rpbarnes/PI_Blackbox/PCB/FAB_Files/Assembled_Pics/bottom001.png

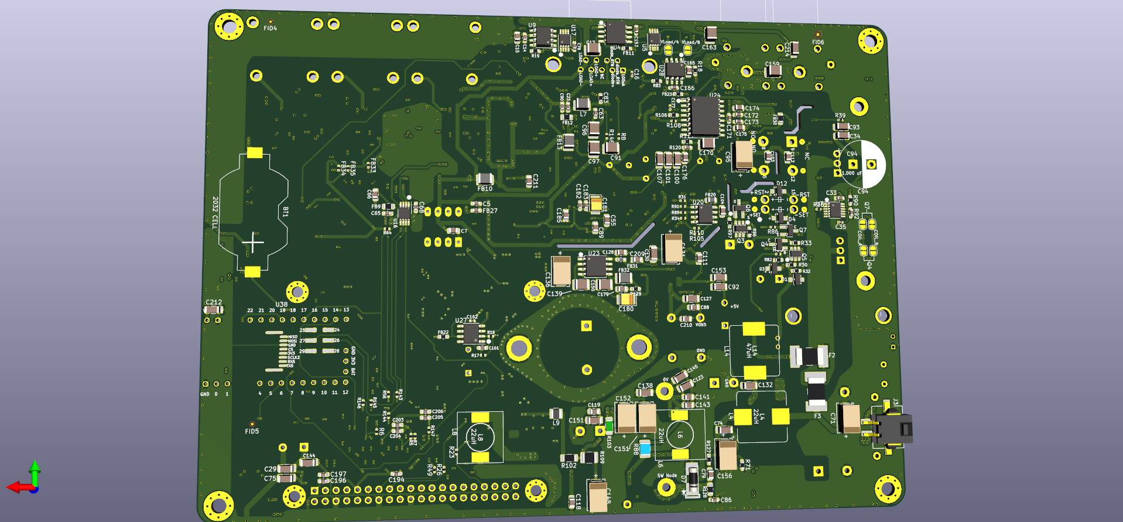
PCB/FAB_Files/Assembled_Pics/bottom001.png
