rpbarnes/PI_Blackbox/PCB/FAB_Files/Assembled_Pics/bottom002.png

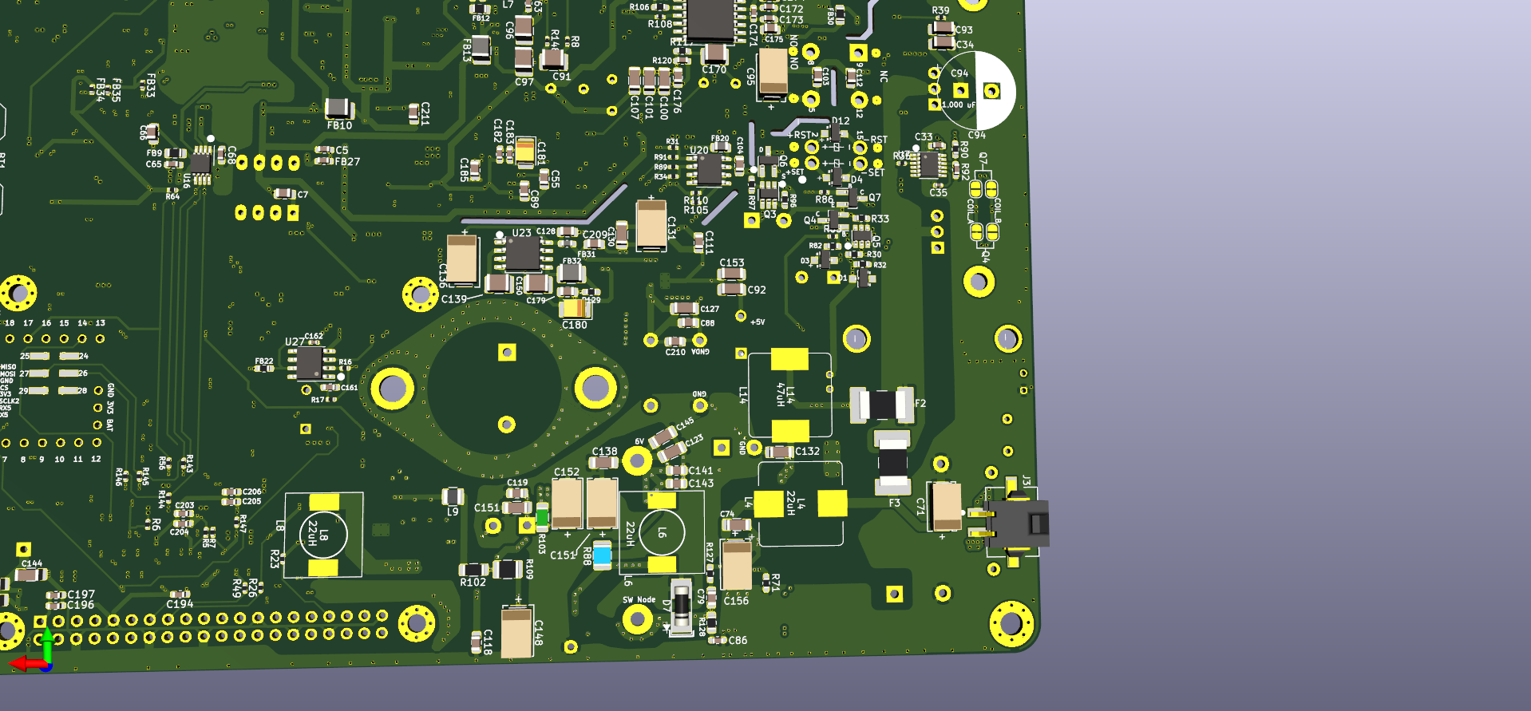
PCB/FAB_Files/Assembled_Pics/bottom002.png
