rpbarnes/PI_Blackbox/PCB/FAB_Files/Assembled_Pics/bottom003.png

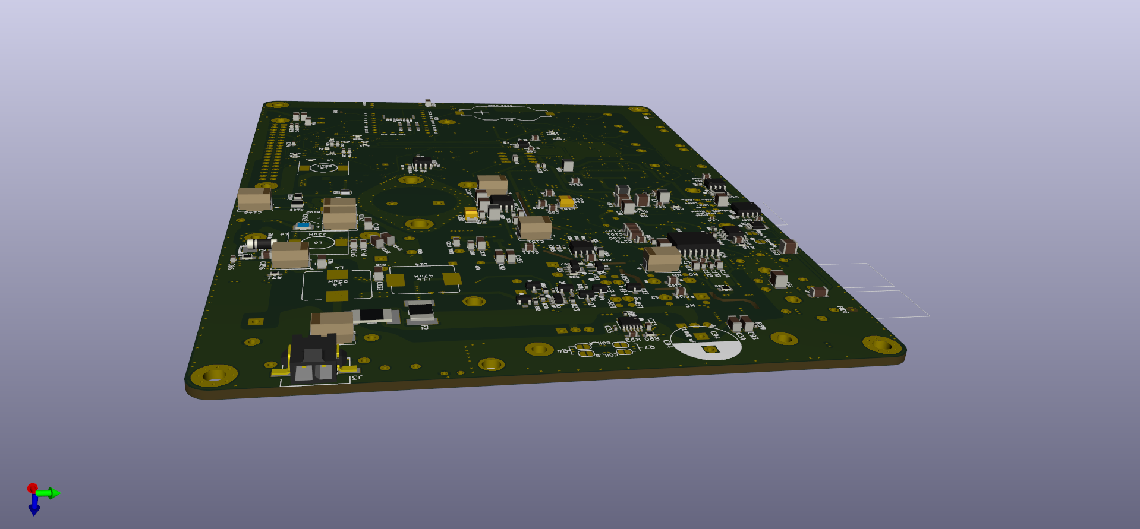
PCB/FAB_Files/Assembled_Pics/bottom003.png
