rpbarnes/PI_Blackbox/PCB/FAB_Files/Assembled_Pics/top001.png

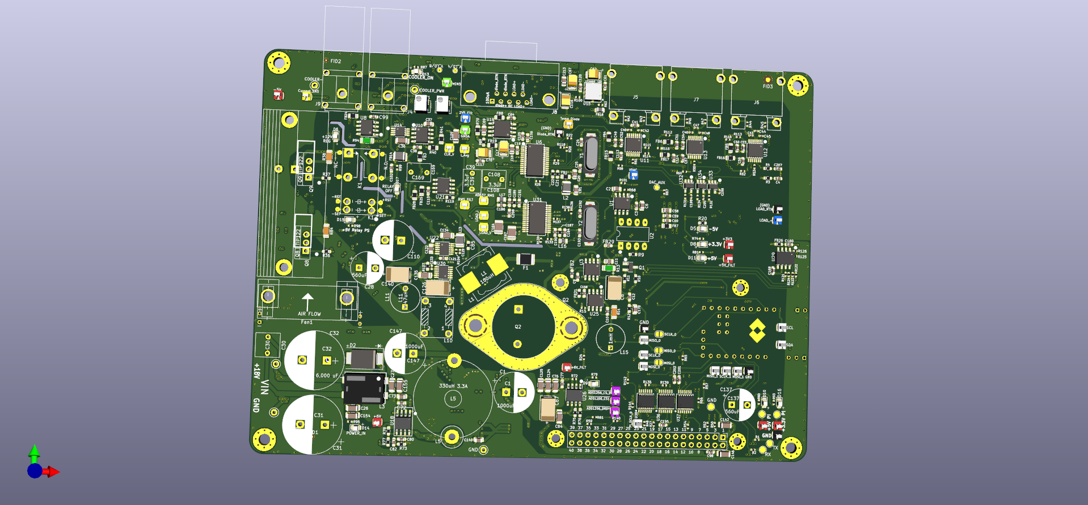
PCB/FAB_Files/Assembled_Pics/top001.png
