rpbarnes/PI_Blackbox/PCB/FAB_Files/Assembled_Pics/top003.png

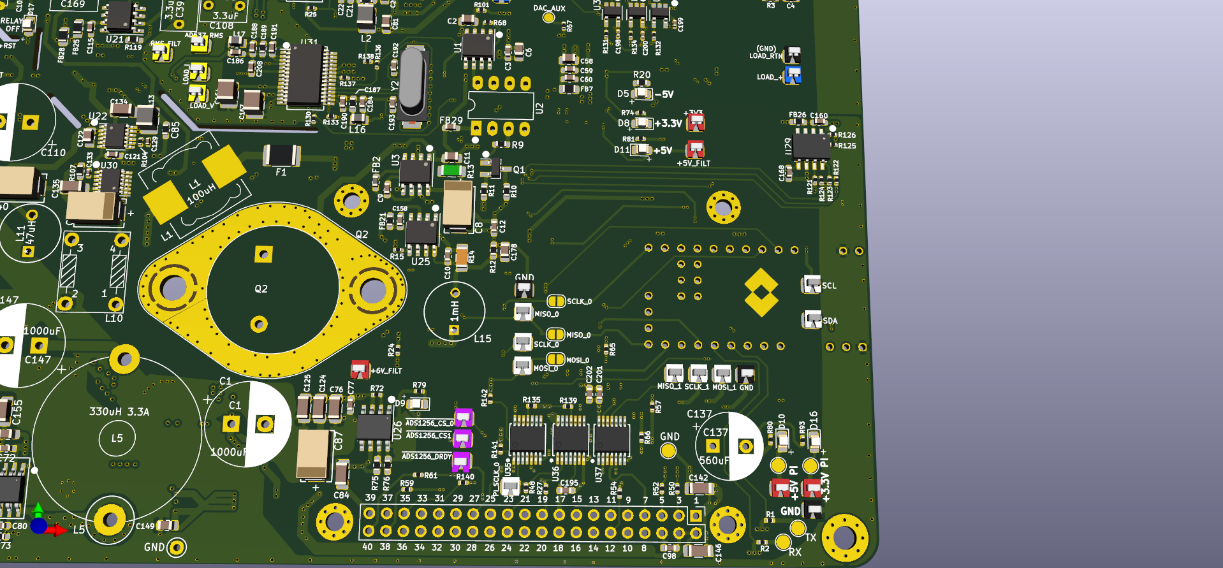
PCB/FAB_Files/Assembled_Pics/top003.png
