rpbarnes/PI_Blackbox/PCB/FAB_Files/Assembled_Pics/top005.png

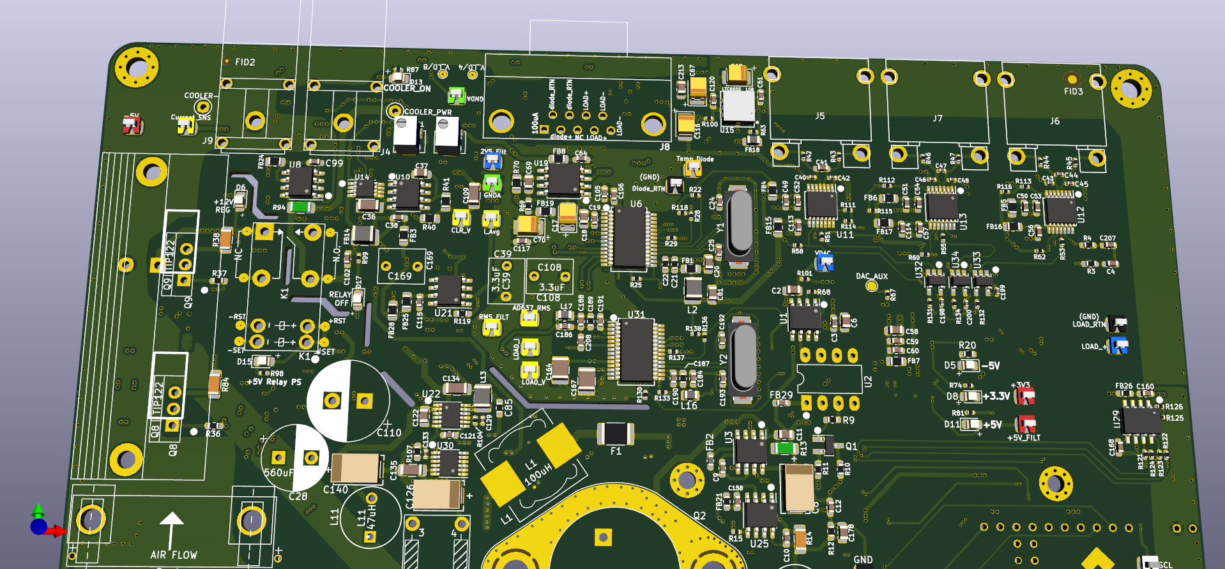
PCB/FAB_Files/Assembled_Pics/top005.png
