rpbarnes/PI_Blackbox/PCB/FAB_Files/Assembled_Pics/top006.png

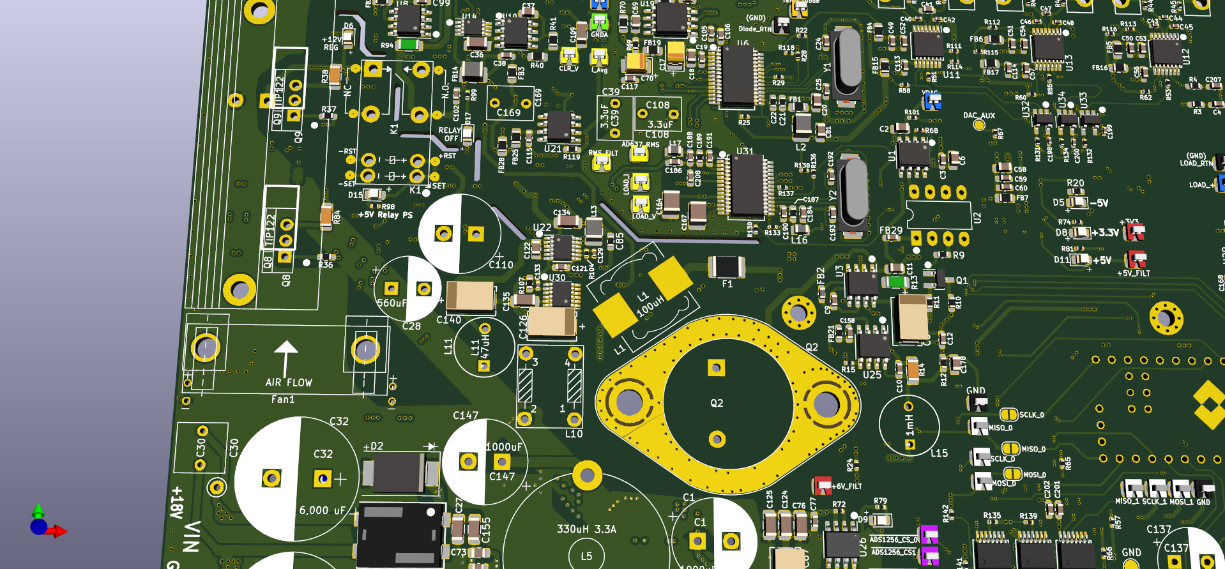
PCB/FAB_Files/Assembled_Pics/top006.png
